kuchaw/proyecto/gps/gps.ino

#include <TinyGPSPlus.h>
#include <WiFi.h>
#include <HTTPClient.h>
#include <WiFiClientSecure.h>

TinyGPSPlus gps;
#define gpsSerial Serial2



//  WiFi credentials
const char* ssid = "Electronica";
const char* password = "KIRCHHOFF24";

// Server endpoint (CHANGE THIS)
const char* serverUrl = "https://cansat1.onrender.com/api/telemetry";

void setup() {
  Serial.begin(115200);
  gpsSerial.begin(9600, SERIAL_8N1, 16, 17);

  Serial.println("Connecting to WiFi...");
  WiFi.begin(ssid, password);

  while (WiFi.status() != WL_CONNECTED) {
    delay(500);
    Serial.print(".");
  }

  Serial.println("\nWiFi connected!");
  Serial.println("Waiting for GPS fix and satellites...");
}

void loop() {

  while (gpsSerial.available() > 0) {
    if (gps.encode(gpsSerial.read())) {
      displayLocationInfo();
      sendToServer();   
    }
  }

  if (millis() > 5000 && gps.charsProcessed() < 10) {
    Serial.println(F("No GPS detected: check wiring."));
    while (true);
  }

  delay(1000);
}

void sendToServer() {
  // only send if GPS is valid
  if (!gps.location.isValid()) {
    Serial.println("GPS not valid, skipping send");
    return;
  }

  if (WiFi.status() == WL_CONNECTED) {
    HTTPClient http;

    http.begin(serverUrl);
    http.addHeader("Content-Type", "application/json");

    // build JSON
    String json = "{";
    json += "\"lat\":" + String(gps.location.lat(), 6) + ",";
    json += "\"lon\":" + String(gps.location.lng(), 6) + ",";
    json += "\"alt\":" + String(gps.altitude.meters()) + ",";
    json += "\"sat\":" + String(gps.satellites.value());
    json += "}";

    WiFiClientSecure client;
    client.setInsecure();

   

    http.begin(client, "https://proyecto-reso.onrender.com/api/telemetry");
    http.addHeader("Content-Type", "application/json");

    int code = http.POST(json);

    Serial.print("HTTP Response: ");
    Serial.println(code);

    http.end();
  } else {
    Serial.println("WiFi disconnected");
  }
}

void displayLocationInfo() {
  Serial.println(F("-------------------------------------"));
  Serial.println("\n Location Info:");

  Serial.print("Latitude:  ");
  Serial.print(gps.location.lat(), 6);
  Serial.print(" ");
  Serial.println(gps.location.rawLat().negative ? "S" : "N");

  Serial.print("Longitude: ");
  Serial.print(gps.location.lng(), 6);
  Serial.print(" ");
  Serial.println(gps.location.rawLng().negative ? "W" : "E");

  Serial.print("Fix Quality: ");
  Serial.println(gps.location.isValid() ? "Valid" : "Invalid");

  Serial.print("Satellites: ");
  Serial.println(gps.satellites.value());

  Serial.print("Altitude:   ");
  Serial.print(gps.altitude.meters());
  Serial.println(" m");

  Serial.print("Speed:      ");
  Serial.print(gps.speed.kmph());
  Serial.println(" km/h");

  Serial.print("Course:     ");
  Serial.print(gps.course.deg());
  Serial.println("°");

  Serial.print("Date:       ");
  if (gps.date.isValid()) {
    Serial.printf("%02d/%02d/%04d\n", gps.date.day(), gps.date.month(), gps.date.year());
  } else {
    Serial.println("Invalid");
  }

  Serial.print("Time (UTC): ");
  if (gps.time.isValid()) {
    Serial.printf("%02d:%02d:%02d\n", gps.time.hour(), gps.time.minute(), gps.time.second());
  } else {
    Serial.println("Invalid");
  }

  Serial.println(F("-------------------------------------"));
  delay(5000);
}
