kuchaw/proyecto/nrf24/transmisor_ultima_prueba_efectiva/modos_de_vuelo/modos_de_vuelo.ino

#include <Wire.h>
#include <math.h>

#include <Adafruit_Sensor.h>
#include <Adafruit_BME680.h>
#include <Adafruit_MPU6050.h>
#include <TinyGPS++.h>
#include <Adafruit_VL53L0X.h>

HardwareSerial CamSerial(1);

// ======================================================
// UART framing ESP32 -> ESP32-CAM
// Frame: 0xAA 0x55 | payload_length | payload | XOR checksum
// ======================================================

const uint8_t UART_SYNC_1 = 0xAA;
const uint8_t UART_SYNC_2 = 0x55;

// ======================================================
// HERMES TELEMETRY PACKET
//
// IMPORTANT:
// alt   = fused relative altitude above launch point [m]
// speed = fused vertical velocity [m/s]
//         positive = climbing, negative = descending
// ======================================================

struct __attribute__((packed)) TelemetryPacket {
  uint32_t counter;
  uint32_t time_ms;

  float lat;
  float lon;
  float alt;            // fused relative altitude [m]
  float speed;          // fused vertical speed [m/s]
  uint8_t sat;

  float temp;           // deg C
  float humidity;       // %
  float pressure;       // hPa
  float gas_kohm;       // kOhm

  int16_t accel_x_cms2;
  int16_t accel_y_cms2;
  int16_t accel_z_cms2;
  int16_t accel_total_cms2;

  uint8_t mode;
};

static_assert(
  sizeof(TelemetryPacket) == 50,
  "TelemetryPacket must be exactly 50 bytes"
);

TelemetryPacket packet;

// ======================================================
// GPS
// ======================================================

#define RXD2 16
#define TXD2 17

TinyGPSPlus gps;

// Last known coordinates are kept only for map continuity.
float lastKnownLat = 0.0f;
float lastKnownLon = 0.0f;
uint8_t lastKnownSat = 0;
bool hasLastKnownGps = false;

// GPS altitude is used only as a secondary Kalman correction.
// We create a relative altitude reference from the first valid,
// stationary samples near the launch point.
const uint8_t GPS_REFERENCE_SAMPLES = 5;
const float GPS_REFERENCE_MAX_BARO_ALT_M = 3.0f;

float gpsReferenceAccumulator = 0.0f;
uint8_t gpsReferenceSampleCount = 0;
float gpsReferenceAltitudeM = NAN;
bool gpsReferenceReady = false;

float lastGpsRelativeAltitudeM = NAN;

// ======================================================
// ESP32-CAM UART
// ======================================================

#define CAM_UART_RX 14
#define CAM_UART_TX 27

// ======================================================
// VL53L0X LiDAR
// Kept for local mission/debug use only.
// ======================================================

Adafruit_VL53L0X lidar = Adafruit_VL53L0X();

bool lidarOk = false;
bool lidarValid = false;
uint16_t lidarDistanceMm = 0;

// ======================================================
// MPU6050
// ======================================================

Adafruit_MPU6050 mpu;

float ax = NAN;
float ay = NAN;
float az = NAN;

float gx = NAN;
float gy = NAN;
float gz = NAN;

float rollDeg = NAN;
float pitchDeg = NAN;
float yawDeg = 0.0f;

float accelTotal = NAN;
float verticalAcceleration = NAN;

bool mpuValid = false;
bool mpuAngleInitialized = false;
bool mpuOk = false;

float gyroOffsetX = 0.0f;
float gyroOffsetY = 0.0f;
float gyroOffsetZ = 0.0f;

const uint32_t MPU_INTERVAL_US = 20000; // 50 Hz
uint32_t lastMpuSampleUs = 0;

const float MPU_FILTER_TAU_S = 0.50f;
const float GRAVITY_MS2 = 9.80665f;

// ======================================================
// BME680
// ======================================================

Adafruit_BME680 bme;

float lastBmeTemp = NAN;
float lastPressure = NAN;
float lastHumidity = NAN;
float lastGas = NAN;

// Barometric reference is calibrated once during setup and then
// remains fixed for the complete mission.
const uint16_t BARO_REFERENCE_SAMPLES = 20;
float pressureReferenceHpa = NAN;
bool baroReferenceReady = false;
float lastBaroAltitudeM = NAN;

// ======================================================
// Vertical 1D Kalman filter
//
// State:
// x[0] = relative altitude [m]
// x[1] = vertical velocity [m/s]
// x[2] = vertical accelerometer bias [m/s^2]
//
// Prediction: MPU6050 vertical acceleration
// Correction: BME680 relative altitude + GPS relative altitude
// ======================================================

class VerticalKalman {
public:
  float x[3];
  float P[3][3];

  // Initial tuning values. These should later be tuned using
  // real static and flight logs.
  float accelNoiseSigma = 0.80f;
  float biasWalkSigma = 0.02f;

  void reset(float initialAltitude = 0.0f, float initialVelocity = 0.0f) {
    x[0] = initialAltitude;
    x[1] = initialVelocity;
    x[2] = 0.0f;

    for (int i = 0; i < 3; i++) {
      for (int j = 0; j < 3; j++) {
        P[i][j] = 0.0f;
      }
    }

    P[0][0] = 4.0f;     // altitude uncertainty
    P[1][1] = 4.0f;     // velocity uncertainty
    P[2][2] = 0.25f;    // acceleration bias uncertainty
  }

  void predict(float measuredVerticalAcceleration, float dt) {
    if (!isfinite(measuredVerticalAcceleration) || dt <= 0.0f || dt > 0.20f) {
      return;
    }

    const float dt2 = dt * dt;
    const float correctedAcceleration = measuredVerticalAcceleration - x[2];

    // State prediction.
    x[0] = x[0] + x[1] * dt + 0.5f * correctedAcceleration * dt2;
    x[1] = x[1] + correctedAcceleration * dt;
    // x[2] follows a random walk and is unchanged in the state prediction.

    const float F[3][3] = {
      {1.0f, dt, -0.5f * dt2},
      {0.0f, 1.0f, -dt},
      {0.0f, 0.0f, 1.0f}
    };

    float FP[3][3] = {};

    for (int i = 0; i < 3; i++) {
      for (int j = 0; j < 3; j++) {
        for (int k = 0; k < 3; k++) {
          FP[i][j] += F[i][k] * P[k][j];
        }
      }
    }

    float newP[3][3] = {};

    for (int i = 0; i < 3; i++) {
      for (int j = 0; j < 3; j++) {
        for (int k = 0; k < 3; k++) {
          // F^T[k][j] = F[j][k]
          newP[i][j] += FP[i][k] * F[j][k];
        }
      }
    }

    const float accelVariance = accelNoiseSigma * accelNoiseSigma;
    const float g0 = 0.5f * dt2;
    const float g1 = dt;

    newP[0][0] += g0 * g0 * accelVariance;
    newP[0][1] += g0 * g1 * accelVariance;
    newP[1][0] += g1 * g0 * accelVariance;
    newP[1][1] += g1 * g1 * accelVariance;

    newP[2][2] += biasWalkSigma * biasWalkSigma * dt;

    for (int i = 0; i < 3; i++) {
      for (int j = 0; j < 3; j++) {
        P[i][j] = newP[i][j];
      }
    }
  }

  void updateAltitude(float measuredAltitude, float measurementVariance) {
    if (!isfinite(measuredAltitude) || measurementVariance <= 0.0f) {
      return;
    }

    // H = [1 0 0]
    const float innovation = measuredAltitude - x[0];
    const float S = P[0][0] + measurementVariance;

    if (!isfinite(S) || S <= 0.0f) {
      return;
    }

    float K[3];
    K[0] = P[0][0] / S;
    K[1] = P[1][0] / S;
    K[2] = P[2][0] / S;

    x[0] += K[0] * innovation;
    x[1] += K[1] * innovation;
    x[2] += K[2] * innovation;

    // Keep the old first row because all P updates must use the
    // covariance matrix from before this measurement correction.
    float oldFirstRow[3] = {
      P[0][0],
      P[0][1],
      P[0][2]
    };

    for (int i = 0; i < 3; i++) {
      for (int j = 0; j < 3; j++) {
        P[i][j] -= K[i] * oldFirstRow[j];
      }
    }

    // Reduce small floating-point asymmetries.
    for (int i = 0; i < 3; i++) {
      for (int j = i + 1; j < 3; j++) {
        const float average = 0.5f * (P[i][j] + P[j][i]);
        P[i][j] = average;
        P[j][i] = average;
      }
    }
  }

  float altitude() const {
    return x[0];
  }

  float verticalVelocity() const {
    return x[1];
  }

  float accelerometerBias() const {
    return x[2];
  }
};

VerticalKalman verticalKalman;
bool kalmanReady = false;

// Measurement tuning values.
const float BARO_ALT_SIGMA_M = 1.5f;
const float GPS_ALT_SIGMA_M = 6.0f;

const float BARO_ALT_VARIANCE = BARO_ALT_SIGMA_M * BARO_ALT_SIGMA_M;
const float GPS_ALT_VARIANCE = GPS_ALT_SIGMA_M * GPS_ALT_SIGMA_M;

// ======================================================
// Timing
// ======================================================

unsigned long lastSendMs = 0;
const unsigned long sendIntervalMs = 750;

// ======================================================
// Mission modes
// ======================================================

enum MissionMode : uint8_t {
  MODE_PRELAUNCH = 0,
  MODE_DESCENT = 1,
  MODE_POST_IMPACT = 2
};

MissionMode currentMode = MODE_PRELAUNCH;


// ======================================================
// Mission transition thresholds
// ======================================================

const float PRELAUNCH_TO_DESCENT_ALT_M = 70.0f;
const float DESCENT_VERTICAL_SPEED_MS = -1.0f;
const uint8_t DESCENT_REQUIRED_SAMPLES = 5;

const unsigned long MIN_DESCENT_TIME_MS = 5000;

const float POST_IMPACT_MAX_ALT_M = 3.0f;
const float POST_IMPACT_MAX_SPEED_MS = 0.35f;
const uint16_t POST_IMPACT_LIDAR_MM = 300;
const uint8_t POST_IMPACT_REQUIRED_SAMPLES = 5;

uint8_t descentCandidateSamples = 0;
uint8_t postImpactCandidateSamples = 0;

unsigned long descentStartMs = 0;
unsigned long postImpactStartMs = 0;
unsigned long missionStartMs = 0;
unsigned long modeStartMs = 0;

// ======================================================
// Function declarations
// ======================================================

void updateGPS();
void updateGpsAltitudeReferenceAndKalman();

void updateEnvironmentalSensors();
bool calibrateBarometricReference(uint16_t samples = BARO_REFERENCE_SAMPLES);
float pressureToRelativeAltitude(float pressureHpa, float referencePressureHpa);

void updateLidar();

void updateMPU6050();
bool calibrateMPU6050(uint16_t samples = 500);
void printMPUReport();
void printMPUAngleReport();

float wrapAngle180(float angleDeg);
float complementaryAngle(float gyroPredictionDeg, float accelAngleDeg, float alpha);
float calculateVerticalAcceleration(float accelX, float accelY, float accelZ,
                                    float rollDegrees, float pitchDegrees);

void printNavigationFilterReport();

int16_t accelToCms2(float accel_ms2);

size_t sendFramedUartPacket(const uint8_t *data, uint8_t length);
void sendTelemetryPacket();
void sendTelemetryCycle();


//declaracion de los modos
void handlePrelaunch();
void handleDescent();
void handlePostImpact();

//declaracion de las condciones para que ccambie de modo
void checkPrelaunchToDescent();
void checkDescentToPostImpact();


void setMissionMode(MissionMode newMode);

// ======================================================
// Mission mode control
// ======================================================
void setMissionMode(MissionMode newMode) {
  if (newMode == currentMode) {
    return;
  }

  currentMode = newMode;
  modeStartMs = millis();

  if (newMode == MODE_PRELAUNCH) {
    descentCandidateSamples = 0;
    postImpactCandidateSamples = 0;
  }

  if (newMode == MODE_DESCENT) {
    descentStartMs = millis();
    postImpactCandidateSamples = 0;

    Serial.println(">>> MODE CHANGE: DESCENT");
  }

  if (newMode == MODE_POST_IMPACT) {
    postImpactStartMs = millis();

    Serial.println(">>> MODE CHANGE: POST_IMPACT");
  }
}
// ======================================================
// Setup
// ======================================================

void setup() {
  Serial.begin(115200);
  delay(1000);

  missionStartMs = millis();
  modeStartMs = missionStartMs;
  currentMode = MODE_PRELAUNCH;

  CamSerial.setRxBufferSize(2048);
  CamSerial.begin(115200, SERIAL_8N1, CAM_UART_RX, CAM_UART_TX);

  Serial.println("ESP32-CAM UART link ready");

  Wire.begin(21, 22);

  Serial2.begin(9600, SERIAL_8N1, RXD2, TXD2);

  // ----------------------------------------------------
  // LiDAR
  // ----------------------------------------------------

  if (!lidar.begin()) {
    Serial.println("VL53L0X LiDAR not detected");
    lidarOk = false;
  } else {
    Serial.println("VL53L0X LiDAR detected");
    lidarOk = true;
  }

  // ----------------------------------------------------
  // BME680
  // ----------------------------------------------------

  if (!bme.begin(0x77)) {
    Serial.println("BME680 not found at 0x77, trying 0x76...");

    if (!bme.begin(0x76)) {
      Serial.println("BME680 not detected");
      while (1) {
        delay(1000);
      }
    }
  }

  bme.setTemperatureOversampling(BME680_OS_8X);
  bme.setHumidityOversampling(BME680_OS_2X);
  bme.setPressureOversampling(BME680_OS_4X);
  bme.setIIRFilterSize(BME680_FILTER_SIZE_3);
  bme.setGasHeater(320, 150);

  Serial.println("BME680 detected");

  // Establish h = 0 m at the launch point.
  if (calibrateBarometricReference()) {
    verticalKalman.reset(0.0f, 0.0f);
    kalmanReady = true;
    Serial.println("Vertical Kalman initialized at h=0 m, v=0 m/s");
  } else {
    Serial.println("WARNING: barometric reference calibration failed");
    kalmanReady = false;
  }

  // ----------------------------------------------------
  // MPU6050
  // ----------------------------------------------------

  if (!mpu.begin()) {
    Serial.println("MPU6050 not detected");
    mpuOk = false;
  } else {
    Serial.println("MPU6050 detected");
    mpuOk = true;

    mpu.setAccelerometerRange(MPU6050_RANGE_8_G);
    mpu.setGyroRange(MPU6050_RANGE_500_DEG);
    mpu.setFilterBandwidth(MPU6050_BAND_21_HZ);

    delay(250);
    calibrateMPU6050();
    updateMPU6050();
  }

  packet.counter = 0;
  packet.time_ms = 0;

  Serial.println();
  Serial.println("======================================");
  Serial.println("Hermes onboard computer ready");
  Serial.print("TelemetryPacket size: ");
  Serial.print(sizeof(TelemetryPacket));
  Serial.println(" bytes");
  Serial.print("Barometric reference hPa: ");
  Serial.println(pressureReferenceHpa, 3);
  Serial.println("alt   = fused relative altitude [m]");
  Serial.println("speed = fused vertical velocity [m/s]");
  Serial.println("======================================");
}

// ======================================================
// Main loop
// ======================================================

void loop() {
  updateGPS();

  // Optional ESP32-CAM return/debug channel.
  while (CamSerial.available()) {
    Serial.write(CamSerial.read());
  }

  uint32_t nowUs = micros();

  if ((uint32_t)(nowUs - lastMpuSampleUs) >= MPU_INTERVAL_US) {
    updateMPU6050();
  }

  unsigned long now = millis();

  if (now - lastSendMs >= sendIntervalMs) {
    lastSendMs = now;

    if (currentMode == MODE_PRELAUNCH) {
      handlePrelaunch();
    } else if (currentMode == MODE_DESCENT) {
      handleDescent();
    } else if (currentMode == MODE_POST_IMPACT) {
      handlePostImpact();
    }
  }
}

// ======================================================
// Mission handlers
// ======================================================
void handlePrelaunch() {
  Serial.println();
  Serial.println("===== PRELAUNCH MODE =====");

  updateEnvironmentalSensors();
  printMPUReport();
  printMPUAngleReport();
  printNavigationFilterReport();
  updateLidar();

  bool gpsOk = gps.location.isValid() && gps.location.age() < 3000;
  bool bmeOk = isfinite(lastBmeTemp) && isfinite(lastPressure) && isfinite(lastHumidity);

  Serial.print("GPS ready: ");
  Serial.println(gpsOk ? "YES" : "NO");

  Serial.print("BME680 ready: ");
  Serial.println(bmeOk ? "YES" : "NO");

  Serial.print("Prelaunch status: ");
  Serial.println((gpsOk && bmeOk && kalmanReady) ? "READY" : "NOT READY");

  checkPrelaunchToDescent();

  sendTelemetryCycle();
}


void handleDescent() {
  Serial.println();
  Serial.println("===== DESCENT MODE =====");

  updateEnvironmentalSensors();
  printMPUReport();
  printMPUAngleReport();
  printNavigationFilterReport();
  updateLidar();

  checkDescentToPostImpact();

  sendTelemetryCycle();
}
void handlePostImpact() {
  Serial.println();
  Serial.println("===== POST IMPACT MODE =====");

  updateEnvironmentalSensors();
  printMPUReport();
  printNavigationFilterReport();

  sendTelemetryCycle();
}

void checkPrelaunchToDescent() {
  if (!kalmanReady) {
    descentCandidateSamples = 0;
    return;
  }

  float altitudeM = verticalKalman.altitude();
  float verticalSpeedMs = verticalKalman.verticalVelocity();

  bool altitudeOk =
    isfinite(altitudeM) &&
    altitudeM > PRELAUNCH_TO_DESCENT_ALT_M;

  bool descendingOk =
    isfinite(verticalSpeedMs) &&
    verticalSpeedMs < DESCENT_VERTICAL_SPEED_MS;

  if (altitudeOk && descendingOk) {
    descentCandidateSamples++;
  } else {
    descentCandidateSamples = 0;
  }

  Serial.print("Descent candidate samples: ");
  Serial.println(descentCandidateSamples);

  if (descentCandidateSamples >= DESCENT_REQUIRED_SAMPLES) {
    setMissionMode(MODE_DESCENT);
  }
}


void checkPrelaunchToDescent() {
  if (!kalmanReady) {
    descentCandidateSamples = 0;
    return;
  }

  float altitudeM = verticalKalman.altitude();
  float verticalSpeedMs = verticalKalman.verticalVelocity();

  bool altitudeOk =
    isfinite(altitudeM) &&
    altitudeM > PRELAUNCH_TO_DESCENT_ALT_M;

  bool descendingOk =
    isfinite(verticalSpeedMs) &&
    verticalSpeedMs < DESCENT_VERTICAL_SPEED_MS;

  if (altitudeOk && descendingOk) {
    descentCandidateSamples++;
  } else {
    descentCandidateSamples = 0;
  }

  Serial.print("Descent candidate samples: ");
  Serial.println(descentCandidateSamples);

  if (descentCandidateSamples >= DESCENT_REQUIRED_SAMPLES) {
    setMissionMode(MODE_DESCENT);
  }
}
// ======================================================
// GPS
// ======================================================

void updateGPS() {
  while (Serial2.available() > 0) {
    gps.encode(Serial2.read());
  }

  updateGpsAltitudeReferenceAndKalman();
}

void updateGpsAltitudeReferenceAndKalman() {
  // Only act when TinyGPS++ reports a new altitude value.
  if (!gps.altitude.isUpdated() || !gps.altitude.isValid()) {
    return;
  }

  const float gpsAltitudeM = (float)gps.altitude.meters();

  if (!isfinite(gpsAltitudeM)) {
    return;
  }

  // Build the GPS reference only from early samples while the barometric
  // estimate still indicates that the CanSat is close to the launch point.
  if (!gpsReferenceReady) {
    const bool nearLaunchPoint =
      !kalmanReady || fabsf(verticalKalman.altitude()) <= GPS_REFERENCE_MAX_BARO_ALT_M;

    if (currentMode == MODE_PRELAUNCH && nearLaunchPoint) {
      gpsReferenceAccumulator += gpsAltitudeM;
      gpsReferenceSampleCount++;

      Serial.print("GPS reference sample ");
      Serial.print(gpsReferenceSampleCount);
      Serial.print("/");
      Serial.print(GPS_REFERENCE_SAMPLES);
      Serial.print(" altitude=");
      Serial.println(gpsAltitudeM, 2);

      if (gpsReferenceSampleCount >= GPS_REFERENCE_SAMPLES) {
        gpsReferenceAltitudeM =
          gpsReferenceAccumulator / (float)gpsReferenceSampleCount;

        gpsReferenceReady = true;

        Serial.print("GPS altitude reference locked: ");
        Serial.print(gpsReferenceAltitudeM, 2);
        Serial.println(" m");
      }
    }

    return;
  }

  lastGpsRelativeAltitudeM = gpsAltitudeM - gpsReferenceAltitudeM;

  if (kalmanReady) {
    verticalKalman.updateAltitude(
      lastGpsRelativeAltitudeM,
      GPS_ALT_VARIANCE
    );
  }
}

// ======================================================
// BME680 / barometric altitude
// ======================================================

bool calibrateBarometricReference(uint16_t samples) {
  if (samples == 0) {
    return false;
  }

  Serial.println();
  Serial.println("===== BAROMETRIC REFERENCE CALIBRATION =====");
  Serial.println("Keep the CanSat at the launch altitude...");

  double pressureSum = 0.0;
  uint16_t validSamples = 0;

  for (uint16_t i = 0; i < samples; i++) {
    if (bme.performReading()) {
      const float pressureHpa = bme.pressure / 100.0f;

      if (isfinite(pressureHpa) && pressureHpa > 100.0f) {
        pressureSum += pressureHpa;
        validSamples++;

        // Keep current environment variables initialized too.
        lastBmeTemp = bme.temperature;
        lastPressure = pressureHpa;
        lastHumidity = bme.humidity;
        lastGas = bme.gas_resistance / 1000.0f;
      }
    }

    delay(20);
  }

  if (validSamples < samples / 2) {
    baroReferenceReady = false;
    return false;
  }

  pressureReferenceHpa = (float)(pressureSum / validSamples);
  baroReferenceReady = true;
  lastBaroAltitudeM = 0.0f;

  Serial.print("Pressure reference: ");
  Serial.print(pressureReferenceHpa, 3);
  Serial.print(" hPa from ");
  Serial.print(validSamples);
  Serial.println(" valid samples");

  return true;
}

float pressureToRelativeAltitude(float pressureHpa, float referencePressureHpa) {
  if (
    !isfinite(pressureHpa) ||
    !isfinite(referencePressureHpa) ||
    pressureHpa <= 0.0f ||
    referencePressureHpa <= 0.0f
  ) {
    return NAN;
  }

  return 44330.0f *
    (1.0f - powf(pressureHpa / referencePressureHpa, 0.19029495f));
}

void updateEnvironmentalSensors() {
  if (bme.performReading()) {
    lastBmeTemp = bme.temperature;
    lastPressure = bme.pressure / 100.0f;
    lastHumidity = bme.humidity;
    lastGas = bme.gas_resistance / 1000.0f;

    if (baroReferenceReady) {
      lastBaroAltitudeM = pressureToRelativeAltitude(
        lastPressure,
        pressureReferenceHpa
      );

      if (kalmanReady && isfinite(lastBaroAltitudeM)) {
        verticalKalman.updateAltitude(
          lastBaroAltitudeM,
          BARO_ALT_VARIANCE
        );
      }
    }
  } else {
    Serial.println("BME680 reading failed");
  }

  Serial.println();
  Serial.println("===== PAYLOAD SENSOR REPORT =====");

  Serial.print("GPS valid: ");
  Serial.println(gps.location.isValid() ? "yes" : "no");

  Serial.print("BME680 Temp C: ");
  Serial.println(lastBmeTemp);

  Serial.print("Pressure hPa: ");
  Serial.println(lastPressure);

  Serial.print("Humidity %: ");
  Serial.println(lastHumidity);

  Serial.print("Gas kOhm: ");
  Serial.println(lastGas);

  Serial.print("Barometric relative altitude m: ");
  Serial.println(lastBaroAltitudeM);
}

// ======================================================
// LiDAR
// ======================================================

void updateLidar() {
  if (!lidarOk) {
    lidarValid = false;
    return;
  }

  VL53L0X_RangingMeasurementData_t measure;
  lidar.rangingTest(&measure, false);

  if (measure.RangeStatus != 4) {
    lidarDistanceMm = measure.RangeMilliMeter;
    lidarValid = true;
  } else {
    lidarValid = false;
  }

  Serial.println();
  Serial.println("===== LIDAR REPORT =====");

  Serial.print("LiDAR valid: ");
  Serial.println(lidarValid ? "YES" : "NO");

  Serial.print("Distance mm: ");
  if (lidarValid) {
    Serial.println(lidarDistanceMm);
  } else {
    Serial.println("out of range / invalid");
  }
}

// ======================================================
// MPU6050 calibration
// ======================================================

bool calibrateMPU6050(uint16_t samples) {
  if (!mpuOk || samples == 0) {
    return false;
  }

  Serial.println();
  Serial.println("===== MPU6050 GYRO CALIBRATION =====");
  Serial.println("Keep the CanSat completely still...");

  double sumX = 0.0;
  double sumY = 0.0;
  double sumZ = 0.0;

  sensors_event_t accelEvent;
  sensors_event_t gyroEvent;
  sensors_event_t tempEvent;

  for (uint16_t i = 0; i < samples; i++) {
    mpu.getEvent(&accelEvent, &gyroEvent, &tempEvent);

    sumX += gyroEvent.gyro.x;
    sumY += gyroEvent.gyro.y;
    sumZ += gyroEvent.gyro.z;

    delay(5);
  }

  gyroOffsetX = (float)(sumX / samples);
  gyroOffsetY = (float)(sumY / samples);
  gyroOffsetZ = (float)(sumZ / samples);

  mpuAngleInitialized = false;
  lastMpuSampleUs = micros();

  Serial.print("Gyro offset X rad/s: ");
  Serial.println(gyroOffsetX, 6);

  Serial.print("Gyro offset Y rad/s: ");
  Serial.println(gyroOffsetY, 6);

  Serial.print("Gyro offset Z rad/s: ");
  Serial.println(gyroOffsetZ, 6);

  Serial.println("MPU6050 gyro calibration complete");

  return true;
}

// ======================================================
// MPU6050 angle helpers
// ======================================================

float wrapAngle180(float angleDeg) {
  while (angleDeg > 180.0f) {
    angleDeg -= 360.0f;
  }

  while (angleDeg < -180.0f) {
    angleDeg += 360.0f;
  }

  return angleDeg;
}

float complementaryAngle(float gyroPredictionDeg, float accelAngleDeg, float alpha) {
  float errorDeg = wrapAngle180(accelAngleDeg - gyroPredictionDeg);
  return wrapAngle180(gyroPredictionDeg + (1.0f - alpha) * errorDeg);
}

float calculateVerticalAcceleration(
  float accelX,
  float accelY,
  float accelZ,
  float rollDegrees,
  float pitchDegrees
) {
  if (
    !isfinite(accelX) ||
    !isfinite(accelY) ||
    !isfinite(accelZ) ||
    !isfinite(rollDegrees) ||
    !isfinite(pitchDegrees)
  ) {
    return NAN;
  }

  const float DEG_TO_RAD_F = 0.017453292519943295f;

  const float roll = rollDegrees * DEG_TO_RAD_F;
  const float pitch = pitchDegrees * DEG_TO_RAD_F;

  const float sinRoll = sinf(roll);
  const float cosRoll = cosf(roll);
  const float sinPitch = sinf(pitch);
  const float cosPitch = cosf(pitch);

  // Projection of the accelerometer's specific force onto the
  // world vertical axis. With the CanSat still and level this is +g.
  const float verticalSpecificForce =
      -sinPitch * accelX
      + sinRoll * cosPitch * accelY
      + cosRoll * cosPitch * accelZ;

  // Physical vertical acceleration:
  // stationary -> 0 m/s^2
  // upward acceleration -> positive
  // free fall -> approximately -9.81 m/s^2
  return verticalSpecificForce - GRAVITY_MS2;
}

// ======================================================
// MPU6050 update + Kalman prediction
// ======================================================

void updateMPU6050() {
  if (!mpuOk) {
    mpuValid = false;
    return;
  }

  sensors_event_t accelEvent;
  sensors_event_t gyroEvent;
  sensors_event_t tempEvent;

  mpu.getEvent(&accelEvent, &gyroEvent, &tempEvent);

  uint32_t nowUs = micros();
  float dt = 0.0f;

  if (lastMpuSampleUs != 0) {
    dt = (uint32_t)(nowUs - lastMpuSampleUs) / 1000000.0f;
  }

  lastMpuSampleUs = nowUs;

  ax = accelEvent.acceleration.x;
  ay = accelEvent.acceleration.y;
  az = accelEvent.acceleration.z;

  gx = gyroEvent.gyro.x - gyroOffsetX;
  gy = gyroEvent.gyro.y - gyroOffsetY;
  gz = gyroEvent.gyro.z - gyroOffsetZ;

  accelTotal = sqrtf((ax * ax) + (ay * ay) + (az * az));

  float accRollDeg = atan2f(ay, az) * 180.0f / PI;
  float accPitchDeg = atan2f(-ax, sqrtf((ay * ay) + (az * az))) * 180.0f / PI;

  const float RAD_TO_DEG_F = 57.2957795f;

  float gyroXDegS = gx * RAD_TO_DEG_F;
  float gyroYDegS = gy * RAD_TO_DEG_F;
  float gyroZDegS = gz * RAD_TO_DEG_F;

  if (!mpuAngleInitialized) {
    rollDeg = accRollDeg;
    pitchDeg = accPitchDeg;
    yawDeg = 0.0f;
    mpuAngleInitialized = true;
  }
  else if (dt > 0.0f && dt <= 0.20f) {
    float alpha = MPU_FILTER_TAU_S / (MPU_FILTER_TAU_S + dt);

    float rollPrediction = wrapAngle180(rollDeg + gyroXDegS * dt);
    float pitchPrediction = wrapAngle180(pitchDeg + gyroYDegS * dt);

    rollDeg = complementaryAngle(rollPrediction, accRollDeg, alpha);
    pitchDeg = complementaryAngle(pitchPrediction, accPitchDeg, alpha);
    yawDeg = wrapAngle180(yawDeg + gyroZDegS * dt);
  }
  else if (dt > 0.20f) {
    rollDeg = accRollDeg;
    pitchDeg = accPitchDeg;
  }

  mpuValid =
    isfinite(ax) &&
    isfinite(ay) &&
    isfinite(az) &&
    isfinite(gx) &&
    isfinite(gy) &&
    isfinite(gz) &&
    isfinite(accelTotal) &&
    isfinite(rollDeg) &&
    isfinite(pitchDeg);

  verticalAcceleration = calculateVerticalAcceleration(
    ax,
    ay,
    az,
    rollDeg,
    pitchDeg
  );

  if (
    kalmanReady &&
    mpuValid &&
    isfinite(verticalAcceleration) &&
    dt > 0.0f &&
    dt <= 0.20f
  ) {
    verticalKalman.predict(verticalAcceleration, dt);
  }
}

// ======================================================
// MPU / navigation debug
// ======================================================

void printMPUReport() {
  Serial.println();
  Serial.println("===== MPU6050 REPORT =====");

  if (!mpuOk) {
    Serial.println("MPU6050 not available");
    return;
  }

  Serial.print("Accel m/s^2: ");
  Serial.print(ax);
  Serial.print(", ");
  Serial.print(ay);
  Serial.print(", ");
  Serial.println(az);

  Serial.print("Gyro corrected rad/s: ");
  Serial.print(gx, 4);
  Serial.print(", ");
  Serial.print(gy, 4);
  Serial.print(", ");
  Serial.println(gz, 4);

  Serial.print("Accel total m/s^2: ");
  Serial.println(accelTotal);

  Serial.print("Vertical acceleration m/s^2: ");
  Serial.println(verticalAcceleration);
}

void printMPUAngleReport() {
  Serial.println();
  Serial.println("===== MPU ANGLE REPORT =====");

  Serial.print("Roll deg: ");
  Serial.println(rollDeg);

  Serial.print("Pitch deg: ");
  Serial.println(pitchDeg);

  Serial.print("Yaw deg (relative): ");
  Serial.println(yawDeg);

  Serial.print("MPU valid: ");
  Serial.println(mpuValid ? "YES" : "NO");
}

void printNavigationFilterReport() {
  Serial.println();
  Serial.println("===== VERTICAL KALMAN REPORT =====");

  Serial.print("Baro altitude m: ");
  if (isfinite(lastBaroAltitudeM)) {
    Serial.println(lastBaroAltitudeM, 2);
  } else {
    Serial.println("N/A");
  }

  Serial.print("GPS reference: ");
  Serial.println(gpsReferenceReady ? "READY" : "NOT READY");

  Serial.print("GPS relative altitude m: ");
  if (isfinite(lastGpsRelativeAltitudeM)) {
    Serial.println(lastGpsRelativeAltitudeM, 2);
  } else {
    Serial.println("N/A");
  }

  Serial.print("Vertical acceleration m/s^2: ");
  if (isfinite(verticalAcceleration)) {
    Serial.println(verticalAcceleration, 3);
  } else {
    Serial.println("N/A");
  }

  if (!kalmanReady) {
    Serial.println("Kalman: NOT READY");
    return;
  }

  Serial.print("Kalman altitude m: ");
  Serial.println(verticalKalman.altitude(), 2);

  Serial.print("Kalman vertical speed m/s: ");
  Serial.println(verticalKalman.verticalVelocity(), 2);

  Serial.print("Kalman accel bias m/s^2: ");
  Serial.println(verticalKalman.accelerometerBias(), 4);
}

// ======================================================
// Acceleration conversion
// m/s^2 -> cm/s^2
// -32768 is reserved as invalid.
// ======================================================

int16_t accelToCms2(float accel_ms2) {
  if (!isfinite(accel_ms2)) {
    return -32768;
  }

  float scaled = accel_ms2 * 100.0f;

  if (scaled > 32767.0f) {
    scaled = 32767.0f;
  }

  if (scaled < -32767.0f) {
    scaled = -32767.0f;
  }

  return (int16_t)lroundf(scaled);
}

// ======================================================
// UART frame writer
// ======================================================

size_t sendFramedUartPacket(const uint8_t *data, uint8_t length) {
  uint8_t checksum = length;

  for (uint8_t i = 0; i < length; i++) {
    checksum ^= data[i];
  }

  size_t totalSent = 0;

  totalSent += CamSerial.write(UART_SYNC_1);
  totalSent += CamSerial.write(UART_SYNC_2);
  totalSent += CamSerial.write(length);
  totalSent += CamSerial.write(data, length);
  totalSent += CamSerial.write(checksum);

  return totalSent;
}

// ======================================================
// Single telemetry packet
// ======================================================

void sendTelemetryPacket() {
  const bool gpsPositionOk = gps.location.isValid() && gps.location.age() < 3000;

  packet.counter++;
  packet.time_ms = millis() - missionStartMs;

  // GPS remains responsible for geographic coordinates and satellite count.
  if (gpsPositionOk) {
    packet.lat = (float)gps.location.lat();
    packet.lon = (float)gps.location.lng();

    packet.sat = gps.satellites.isValid()
      ? (uint8_t)gps.satellites.value()
      : 0;

    lastKnownLat = packet.lat;
    lastKnownLon = packet.lon;
    lastKnownSat = packet.sat;
    hasLastKnownGps = true;
  }
  else if (hasLastKnownGps) {
    packet.lat = lastKnownLat;
    packet.lon = lastKnownLon;
    packet.sat = lastKnownSat;
  }
  else {
    packet.lat = 0.0f;
    packet.lon = 0.0f;
    packet.sat = 0;
  }

  // Navigation fields now come from the sensor-fusion estimator.
  if (kalmanReady) {
    packet.alt = verticalKalman.altitude();
    packet.speed = verticalKalman.verticalVelocity();
  } else {
    packet.alt = 0.0f;
    packet.speed = 0.0f;
  }

  packet.temp = isfinite(lastBmeTemp) ? lastBmeTemp : -999.0f;
  packet.humidity = isfinite(lastHumidity) ? lastHumidity : -999.0f;
  packet.pressure = isfinite(lastPressure) ? lastPressure : -999.0f;
  packet.gas_kohm = isfinite(lastGas) ? lastGas : -999.0f;

  packet.accel_x_cms2 = accelToCms2(ax);
  packet.accel_y_cms2 = accelToCms2(ay);
  packet.accel_z_cms2 = accelToCms2(az);
  packet.accel_total_cms2 = accelToCms2(accelTotal);

  packet.mode = (uint8_t)currentMode;

  size_t bytesSent = sendFramedUartPacket(
    (const uint8_t *)&packet,
    sizeof(packet)
  );

  Serial.println();
  Serial.println("===== TELEMETRY PACKET =====");

  Serial.print("Counter: ");
  Serial.println(packet.counter);

  Serial.print("Mission time ms: ");
  Serial.println(packet.time_ms);

  Serial.print("Lat: ");
  Serial.println(packet.lat, 6);

  Serial.print("Lon: ");
  Serial.println(packet.lon, 6);

  Serial.print("Fused relative altitude m: ");
  Serial.println(packet.alt, 2);

  Serial.print("Fused vertical speed m/s: ");
  Serial.println(packet.speed, 2);

  Serial.print("Satellites: ");
  Serial.println(packet.sat);

  Serial.print("Temperature C: ");
  Serial.println(packet.temp);

  Serial.print("Humidity %: ");
  Serial.println(packet.humidity);

  Serial.print("Pressure hPa: ");
  Serial.println(packet.pressure);

  Serial.print("Gas kOhm: ");
  Serial.println(packet.gas_kohm);

  Serial.print("Accel X cm/s^2: ");
  Serial.println(packet.accel_x_cms2);

  Serial.print("Accel Y cm/s^2: ");
  Serial.println(packet.accel_y_cms2);

  Serial.print("Accel Z cm/s^2: ");
  Serial.println(packet.accel_z_cms2);

  Serial.print("Accel total cm/s^2: ");
  Serial.println(packet.accel_total_cms2);

  Serial.print("Mission mode: ");
  Serial.println(packet.mode);

  Serial.print("Payload bytes: ");
  Serial.println(sizeof(packet));

  Serial.print("UART frame bytes sent: ");
  Serial.println(bytesSent);
}

void sendTelemetryCycle() {
  sendTelemetryPacket();
}
